olemlong/SmartParts/images/IMG_3073.png

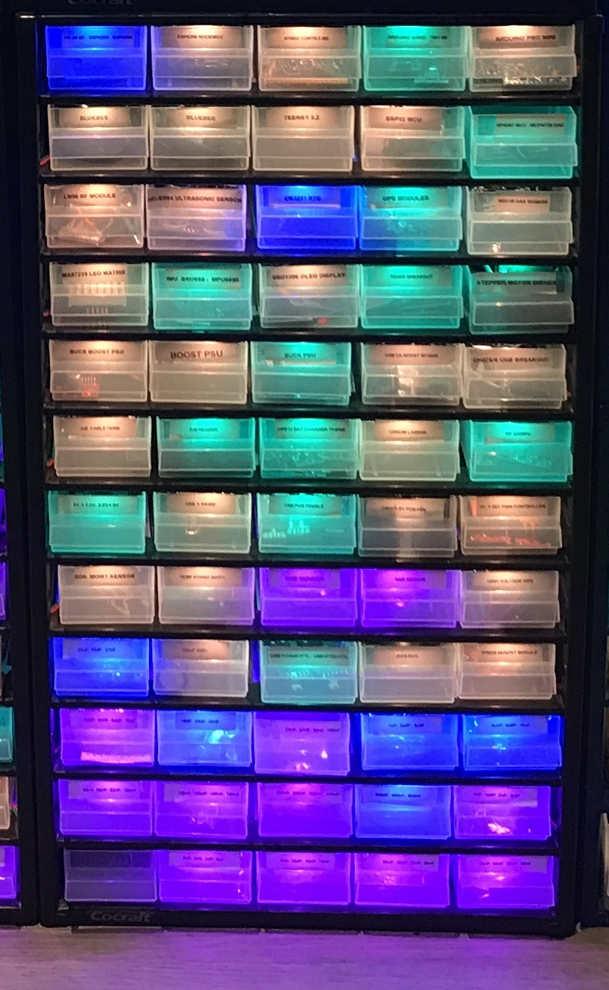
images/IMG_3073.png
